Gabse/PicKitUP/Pictures/20201127_192544.jpg

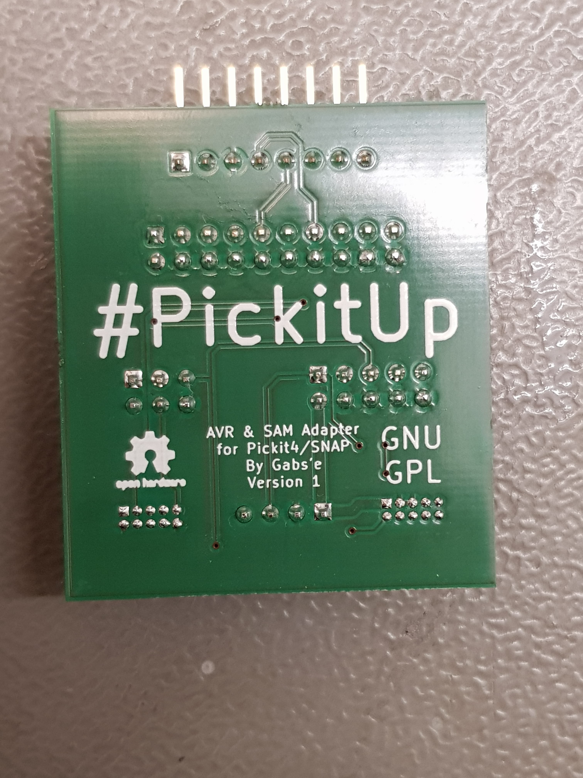
Pictures/20201127_192544.jpg
